patgadget/GuitarSwitcher/Picture/IMG_3309.jpg

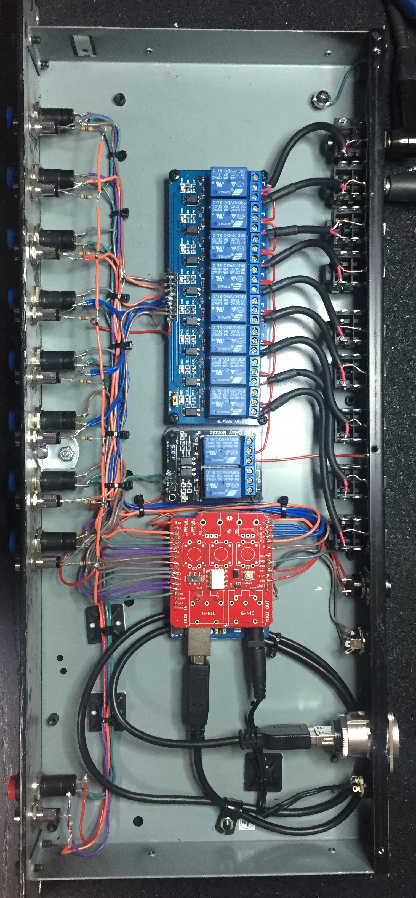
Picture/IMG_3309.jpg
